gurues/PowerMeterDIY_8_Channel/Ayuda_Montaje/Fotos/00_PowerMeter_8CH_F.jpg

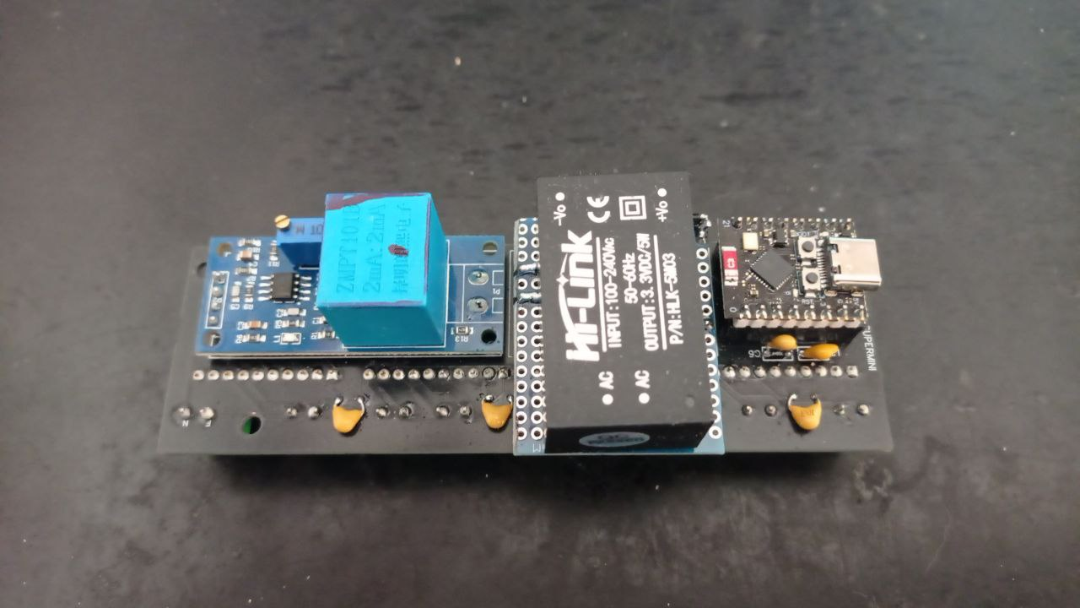
Ayuda_Montaje/Fotos/00_PowerMeter_8CH_F.jpg
