gurues/PowerMeterDIY_8_Channel/Ayuda_Montaje/Fotos/01_PowerMeter_8CH_2.jpg

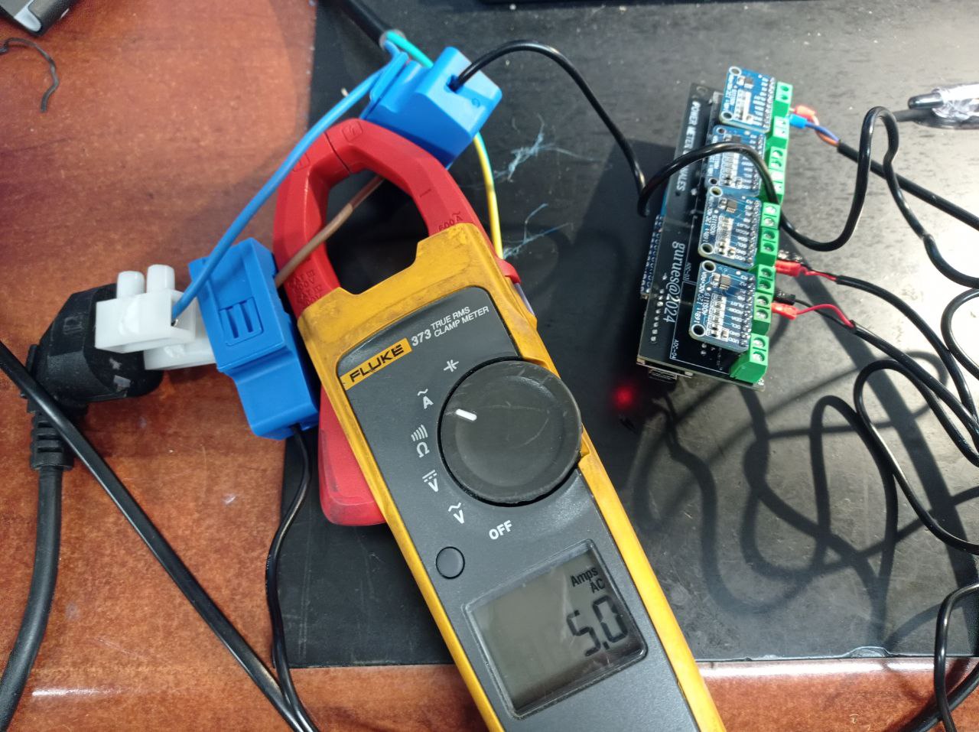
Ayuda_Montaje/Fotos/01_PowerMeter_8CH_2.jpg
