gurues/PowerMeterDIY_8_Channel/Ayuda_Montaje/Fotos/02_PowerMeter_8CH.jpg

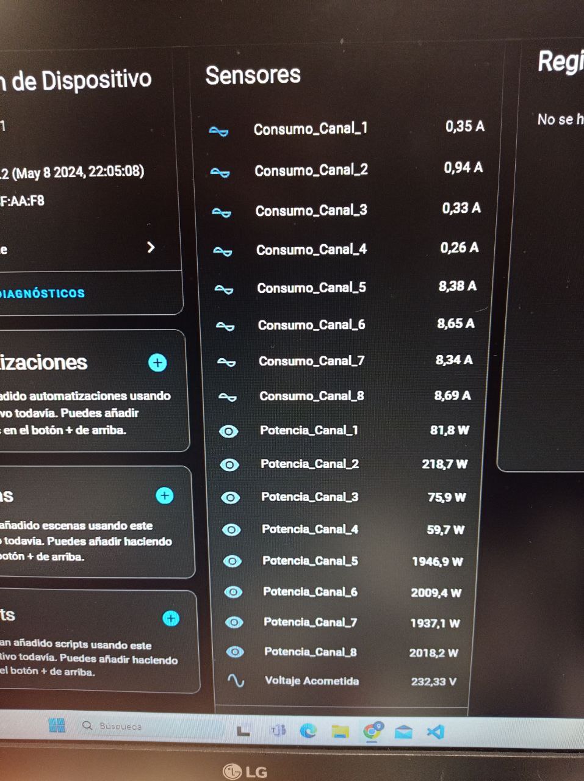
Ayuda_Montaje/Fotos/02_PowerMeter_8CH.jpg
