gurues/PowerMeterDIY_8_Channel/Ayuda_Montaje/Fotos/02_PowerMeter_8CH_1.jpg

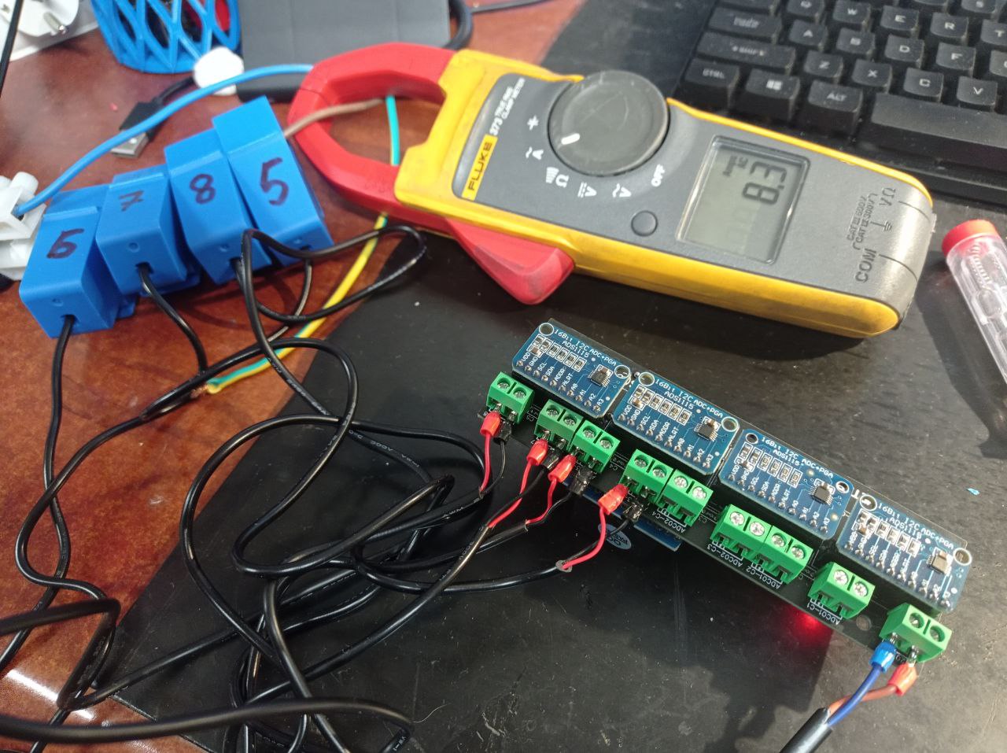
Ayuda_Montaje/Fotos/02_PowerMeter_8CH_1.jpg
