gurues/PowerMeterDIY_8_Channel/Ayuda_Montaje/Placa_Front.png

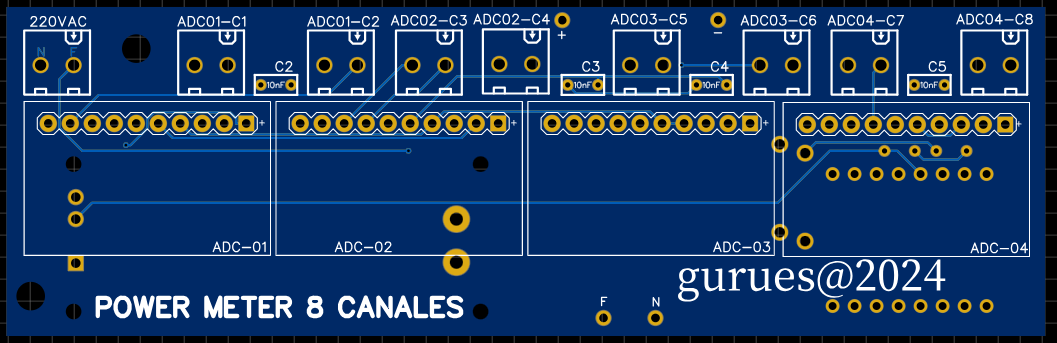
Ayuda_Montaje/Placa_Front.png
